jurjen96/coreXY/Mechanical/Printable Files/X-connector-right.stl

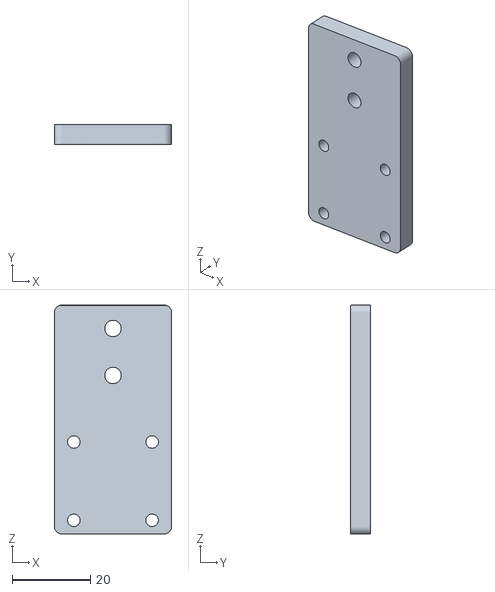
[picture p19: CAD file, 2018-01-07]
Mechanical/Printable Files/X-connector-right.stl
30.0 x 5.00 x 58.5
