jurjen96/coreXY/Mechanical/Printable Files/holder-LCD-screen.stl

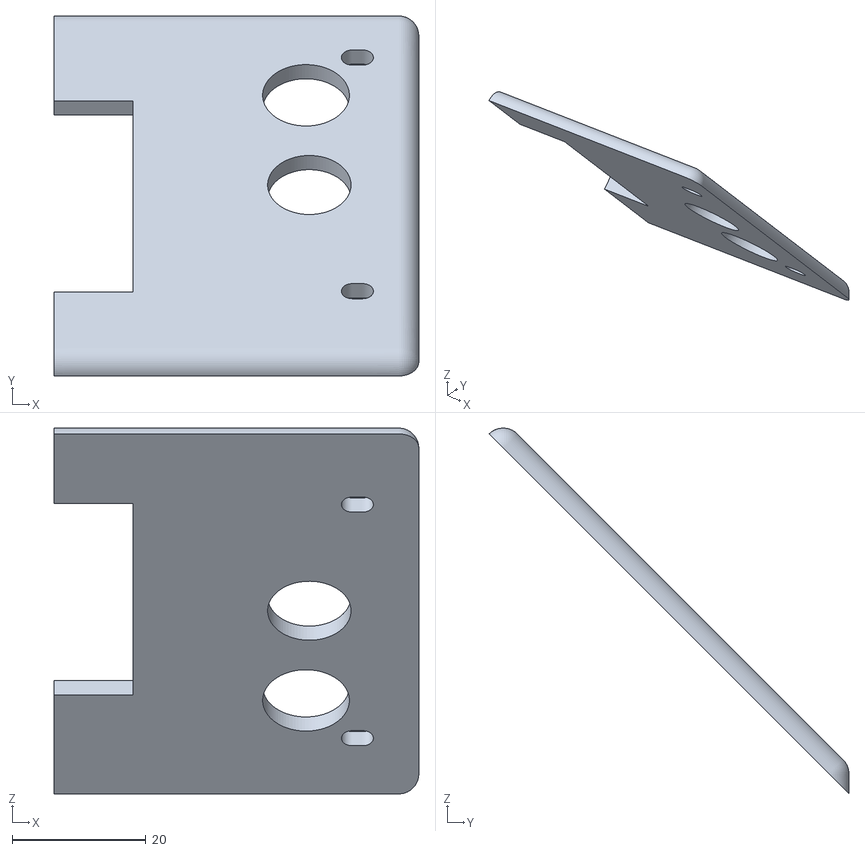
[picture p20: CAD file, 2018-01-07]
Mechanical/Printable Files/holder-LCD-screen.stl
54.6 x 53.9 x 54.8
