jurjen96/coreXY/Mechanical/Printable Files/holder-GT2-x-carriage-left.stl

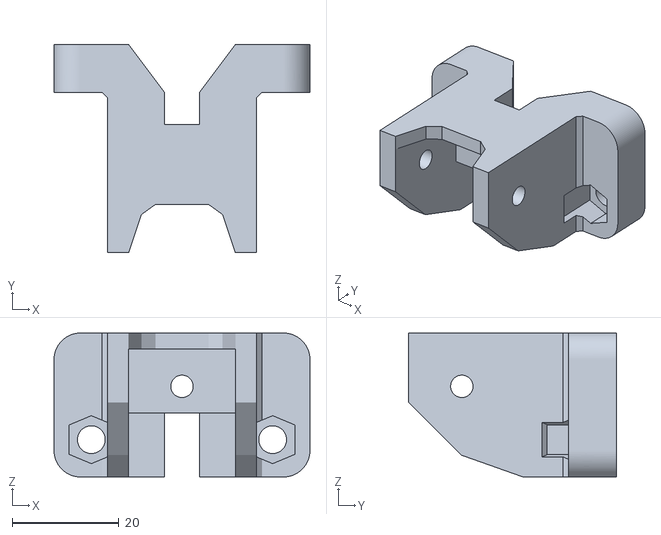
[picture p21: CAD file, 2018-01-07]
Mechanical/Printable Files/holder-GT2-x-carriage-left.stl
48.0 x 39.0 x 27.0
