jurjen96/coreXY/Mechanical/Printable Files/holder-LMF8LUU-z-axis-v2.stl

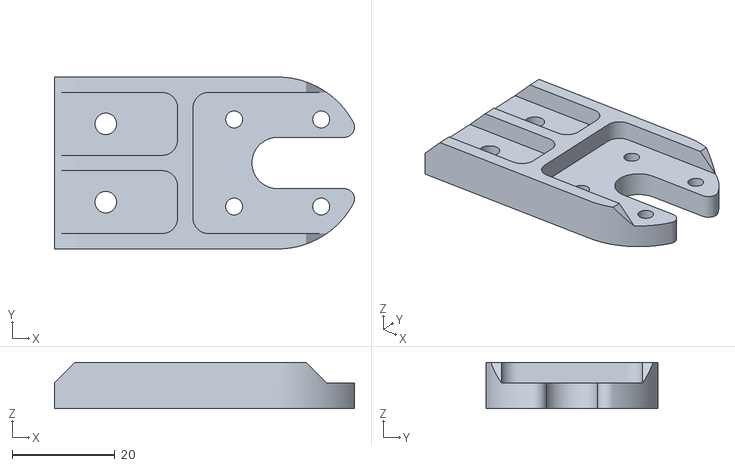
[picture p22: CAD file, 2018-01-07]
Mechanical/Printable Files/holder-LMF8LUU-z-axis-v2.stl
58.5 x 33.5 x 9.00
