jurjen96/coreXY/Mechanical/Printable Files/wheel-mount-x-axis.stl

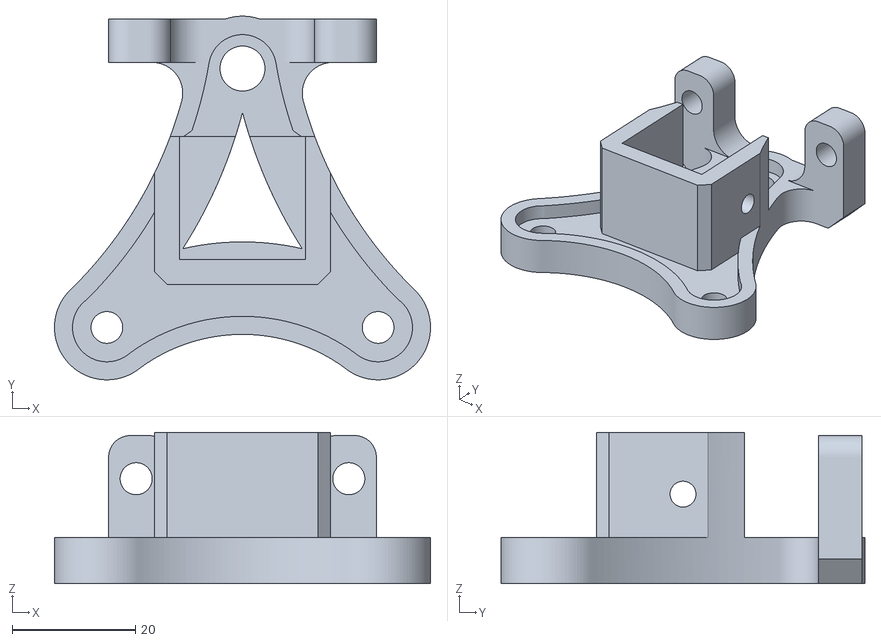
[picture p23: CAD file, 2018-01-07]
Mechanical/Printable Files/wheel-mount-x-axis.stl
61.0 x 59.0 x 24.5
