jurjen96/coreXY/Mechanical/Printable Files/SH8.stl

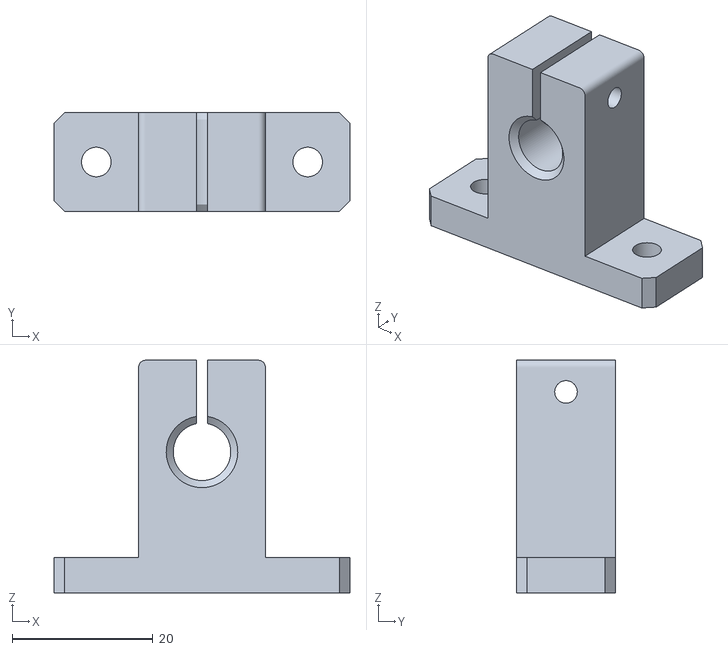
[picture p24: CAD file, 2018-01-07]
Mechanical/Printable Files/SH8.stl
42.0 x 14.0 x 33.0
