jurjen96/coreXY/Mechanical/Printable Files/nema17-mount-bottom-z-axis-v2.stl

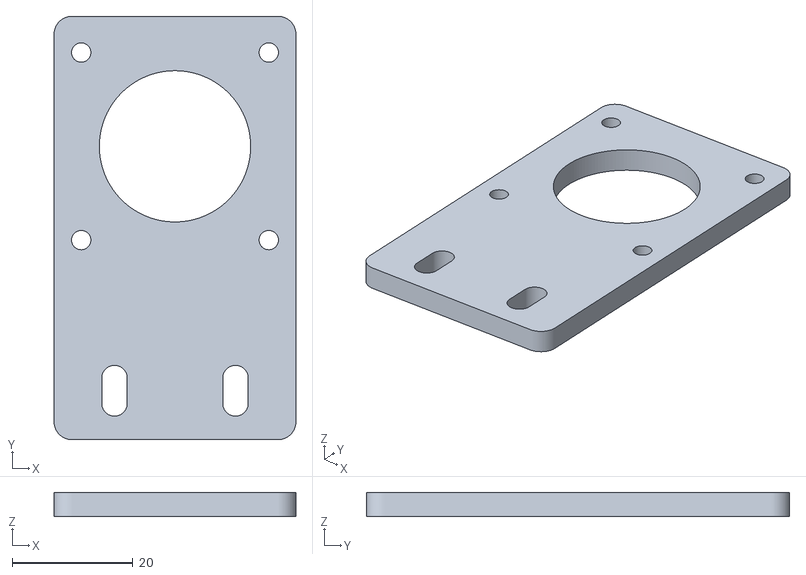
[picture p25: CAD file, 2018-01-07]
Mechanical/Printable Files/nema17-mount-bottom-z-axis-v2.stl
40.0 x 70.0 x 4.00
