jurjen96/coreXY/Mechanical/Printable Files/holder-LMF8LUU-z-axis.stl

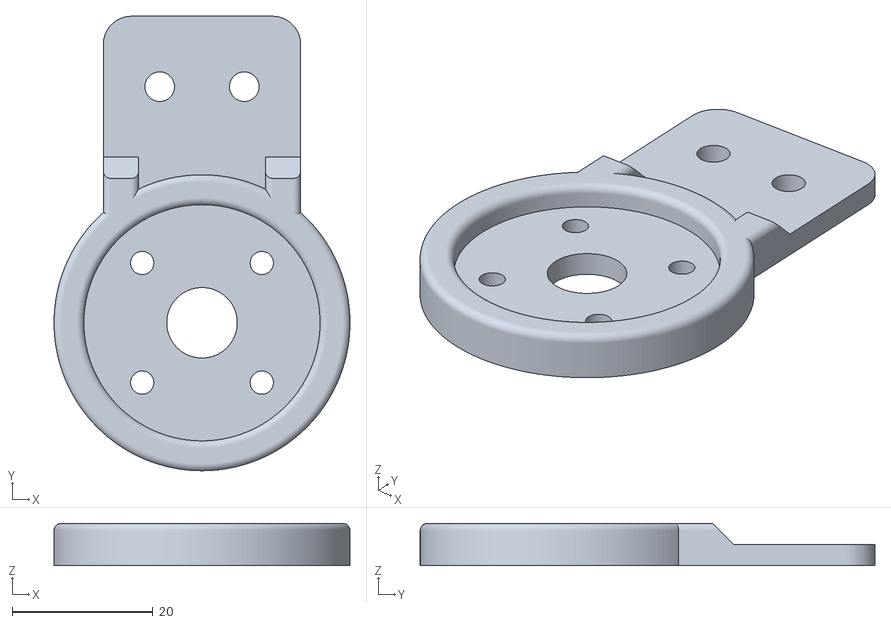
[picture p26: CAD file, 2018-01-07]
Mechanical/Printable Files/holder-LMF8LUU-z-axis.stl
42.0 x 64.5 x 6.00
