jurjen96/coreXY/Mechanical/Printable Files/x-carriage-holder.stl

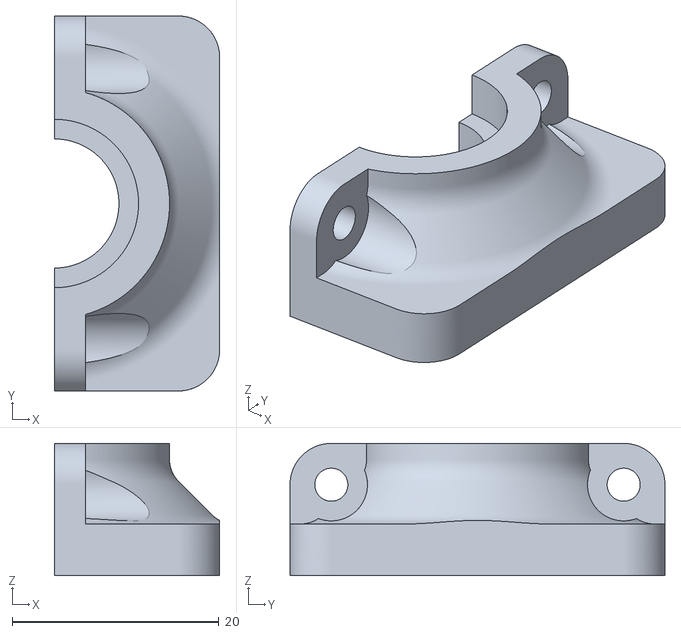
[picture p27: CAD file, 2018-01-07]
Mechanical/Printable Files/x-carriage-holder.stl
16.0 x 36.3 x 12.8
