jurjen96/coreXY/Mechanical/Printable Files/nema17-mount-left.stl

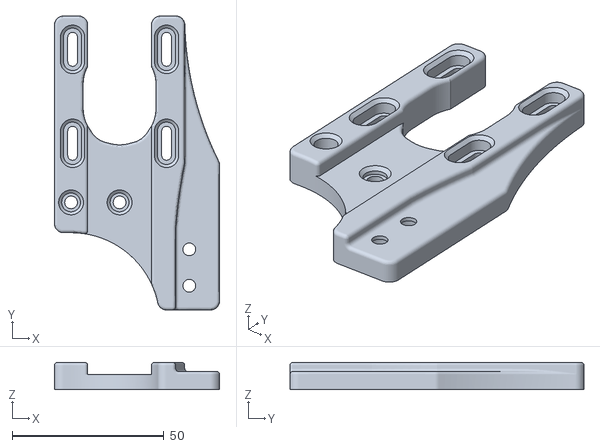
[picture p28: CAD file, 2018-01-07]
Mechanical/Printable Files/nema17-mount-left.stl
54.5 x 97.0 x 9.00
