jurjen96/coreXY/Mechanical/Printable Files/bracket-GT2-right.stl

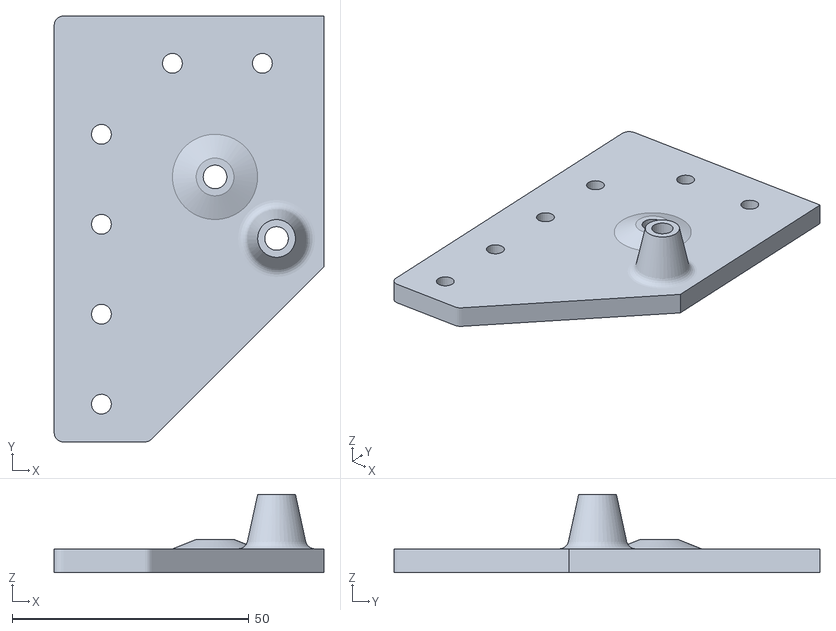
[picture p29: CAD file, 2018-01-07]
Mechanical/Printable Files/bracket-GT2-right.stl
57.0 x 90.0 x 16.5
