jurjen96/coreXY/Mechanical/Printable Files/holder-bearing-z-axis.stl

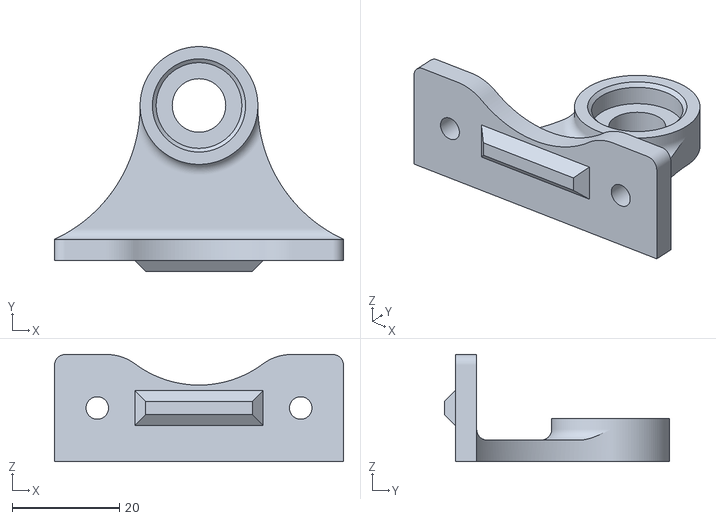
[picture p30: CAD file, 2018-01-07]
Mechanical/Printable Files/holder-bearing-z-axis.stl
54.0 x 42.0 x 20.0
