jurjen96/coreXY/Mechanical/Printable Files/bracket-GT2-left.stl

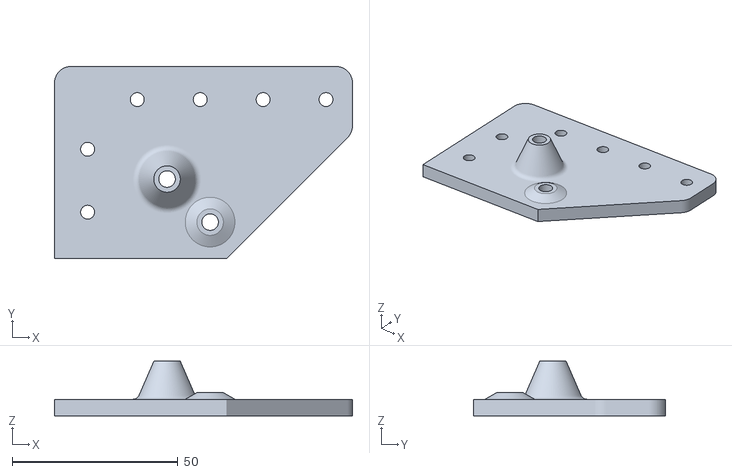
[picture p31: CAD file, 2017-12-17]
Mechanical/Printable Files/bracket-GT2-left.stl
90.0 x 58.0 x 16.5
