jurjen96/coreXY/Mechanical/Printable Files/mount-heated-bed.stl

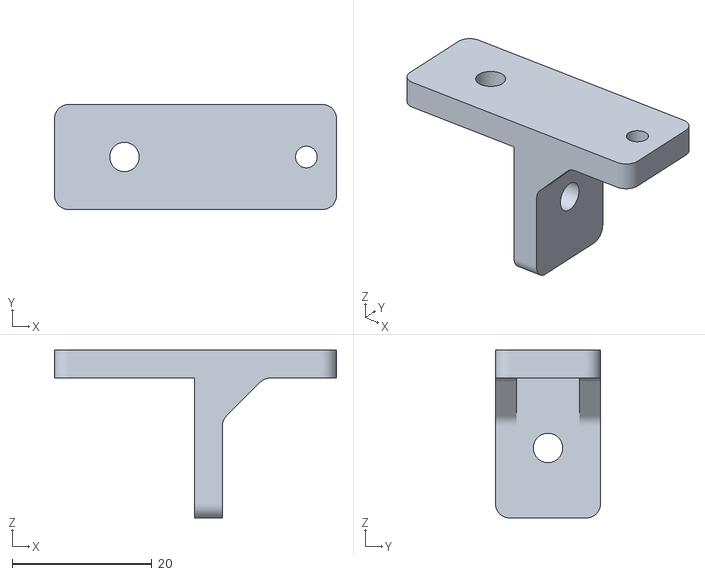
[picture p32: CAD file, 2017-12-17]
Mechanical/Printable Files/mount-heated-bed.stl
40.3 x 15.0 x 24.0
