jurjen96/coreXY/Mechanical/Printable Files/spool-holder.stl

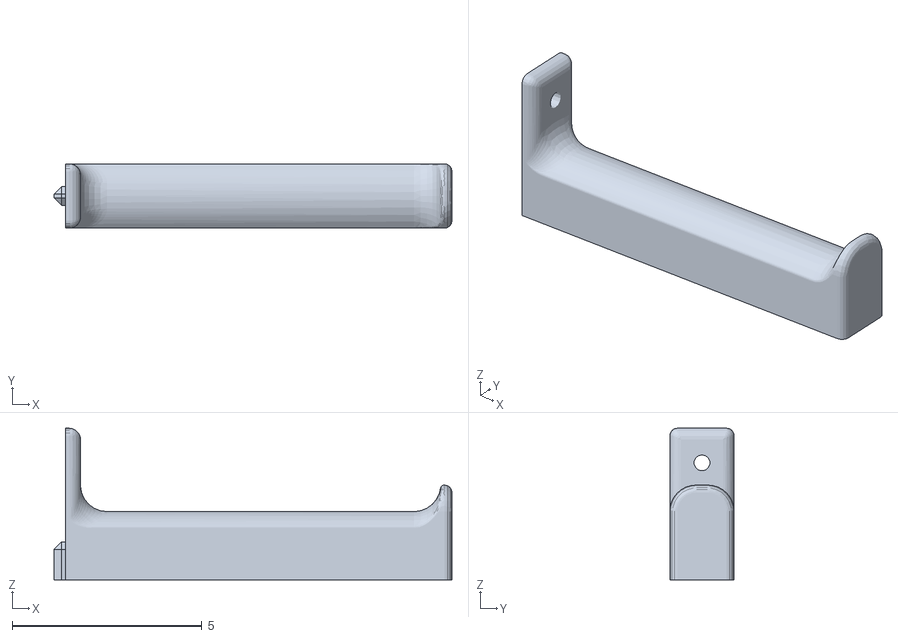
[picture p33: CAD file, 2017-11-05]
Mechanical/Printable Files/spool-holder.stl
10.5 x 1.70 x 4.00
